chooyeonung/obd2-web-diagnostics/firmware/main/wifi_ap.c

#include "wifi_ap.h"
#include <string.h>
#include "esp_wifi.h"
#include "esp_netif.h"
#include "esp_event.h"
#include "esp_log.h"

static const char *TAG = "wifi_ap";

esp_err_t wifi_ap_start(void)
{
    ESP_ERROR_CHECK(esp_netif_init());
    ESP_ERROR_CHECK(esp_event_loop_create_default());
    esp_netif_create_default_wifi_ap();

    wifi_init_config_t cfg = WIFI_INIT_CONFIG_DEFAULT();
    ESP_ERROR_CHECK(esp_wifi_init(&cfg));

    wifi_config_t ap = {
        .ap = {
            .ssid = WIFI_AP_SSID,
            .ssid_len = strlen(WIFI_AP_SSID),
            .password = WIFI_AP_PASS,
            .channel = 6,
            .max_connection = 4,
            .authmode = WIFI_AUTH_WPA2_PSK,
        },
    };

    ESP_ERROR_CHECK(esp_wifi_set_mode(WIFI_MODE_AP));
    ESP_ERROR_CHECK(esp_wifi_set_config(WIFI_IF_AP, &ap));
    ESP_ERROR_CHECK(esp_wifi_start());

    ESP_LOGI(TAG, "SoftAP started: SSID=%s, http://192.168.4.1/", WIFI_AP_SSID);
    return ESP_OK;
}
